Thilos-Projects/NXPCupCar/hardware/NXPModellHallHalterKeil.stl

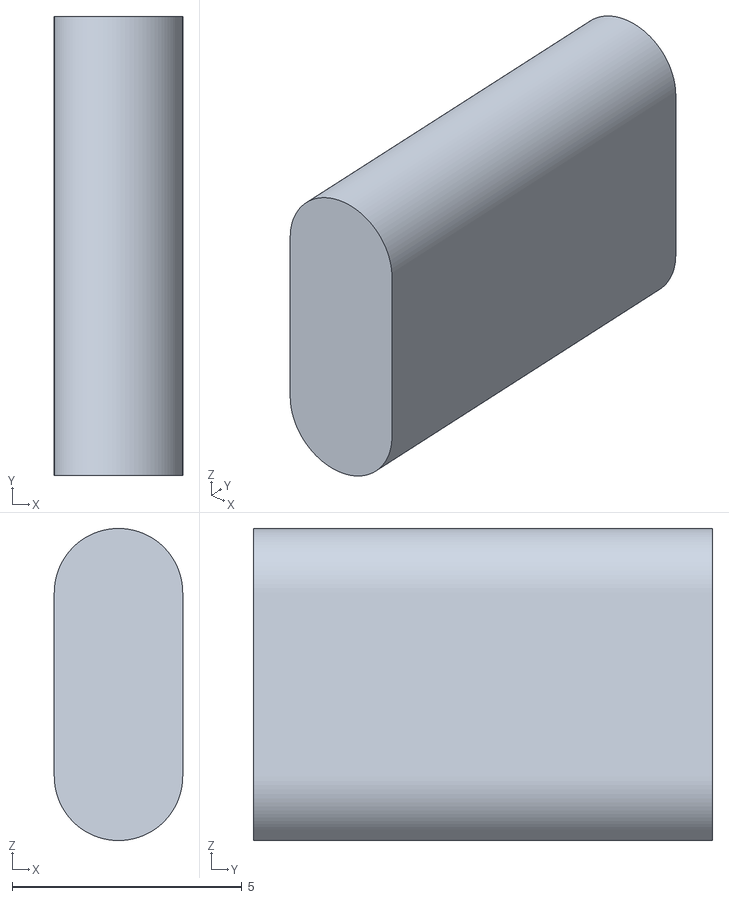
[picture p15: CAD file, 2024-01-16]
hardware/NXPModellHallHalterKeil.stl
2.80 x 10.0 x 6.80
