Thilos-Projects/NXPCupCar/hardware/NXPModellKammeraHalter_30.stl

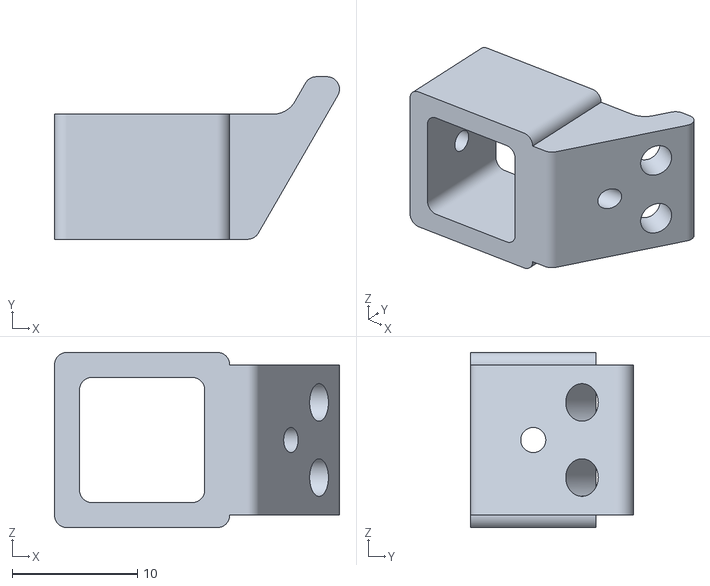
[picture p16: CAD file, 2024-01-16]
hardware/NXPModellKammeraHalter_30.stl
22.8 x 13.0 x 14.0
