Thilos-Projects/NXPCupCar/hardware/NXPModellHallHalter.stl

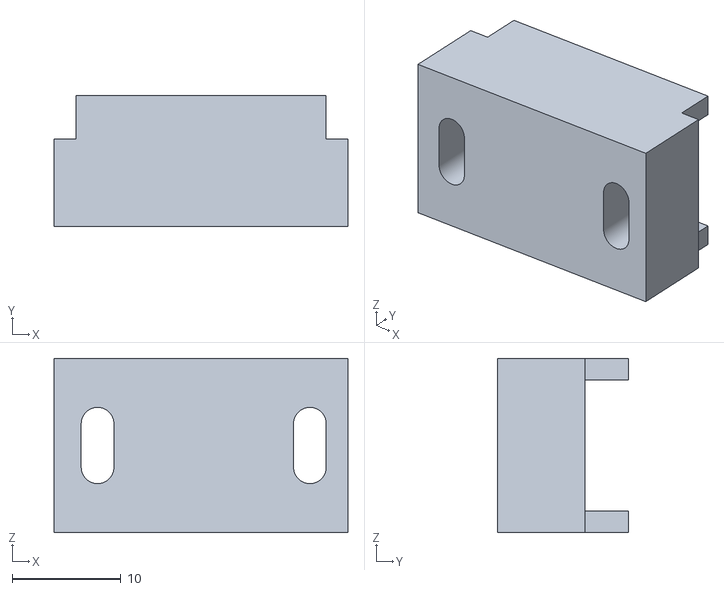
[picture p17: CAD file, 2024-01-16]
hardware/NXPModellHallHalter.stl
27.0 x 12.0 x 16.0
