Thilos-Projects/NXPCupCar/hardware/NXPModellKammeraHalter_15.stl

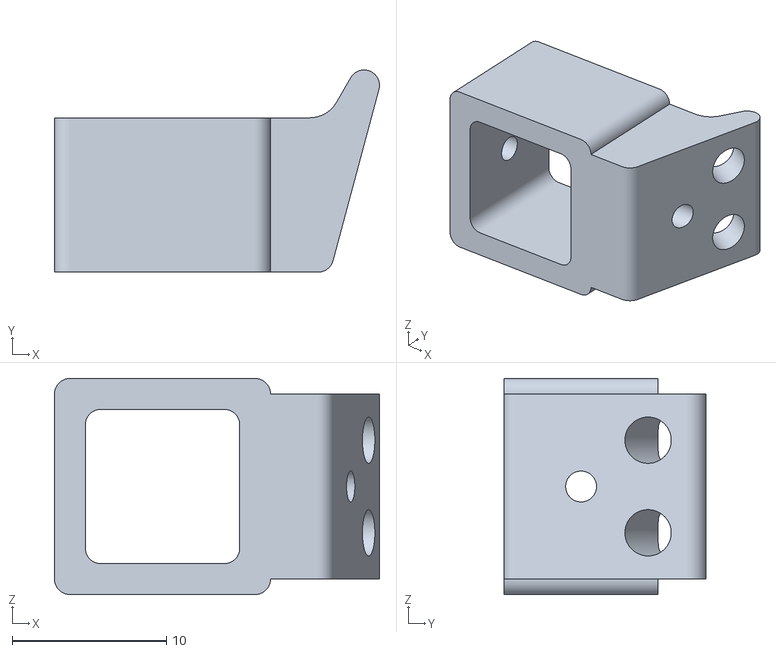
[picture p18: CAD file, 2024-01-16]
hardware/NXPModellKammeraHalter_15.stl
21.1 x 13.1 x 14.0
