Thilos-Projects/NXPCupCar/hardware/NXPModellMagnetSchablone.stl

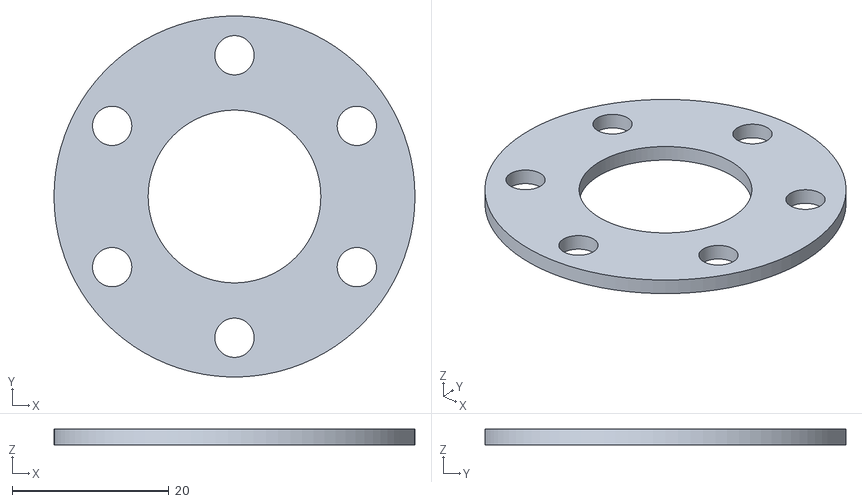
[picture p19: CAD file, 2023-11-28]
hardware/NXPModellMagnetSchablone.stl
46.0 x 46.0 x 2.00
